wjquigs11/coop-feeder/openscad-case/C14641+C14642+C14643+datasheet.png

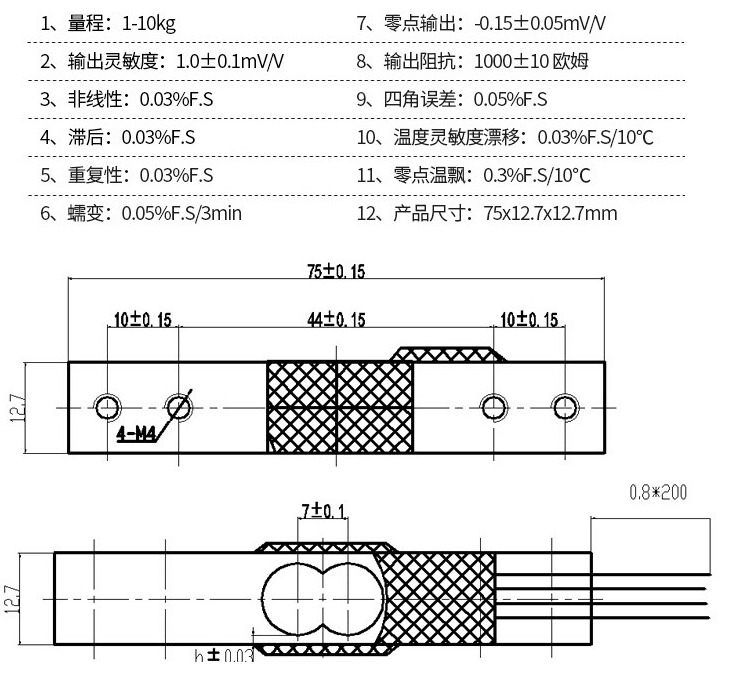
openscad-case/C14641+C14642+C14643+datasheet.png
