wjquigs11/coop-feeder/openscad-case/case.jpg

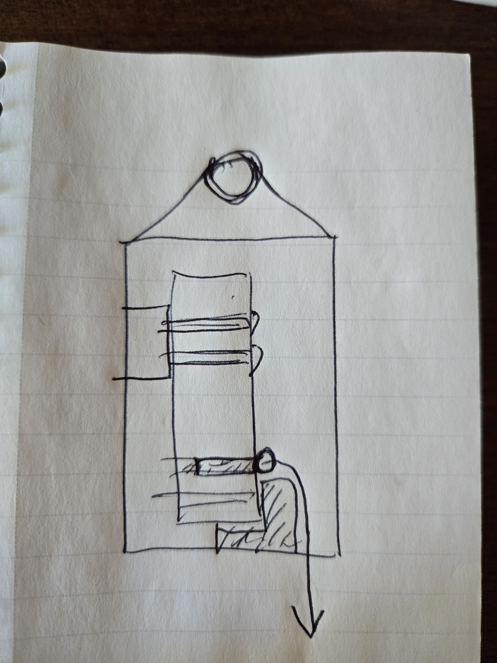
openscad-case/case.jpg
